TKJElectronics/SerialGLCD/PCB/Images for Gerber files/SerialGLCD.boardoutline.ger.png

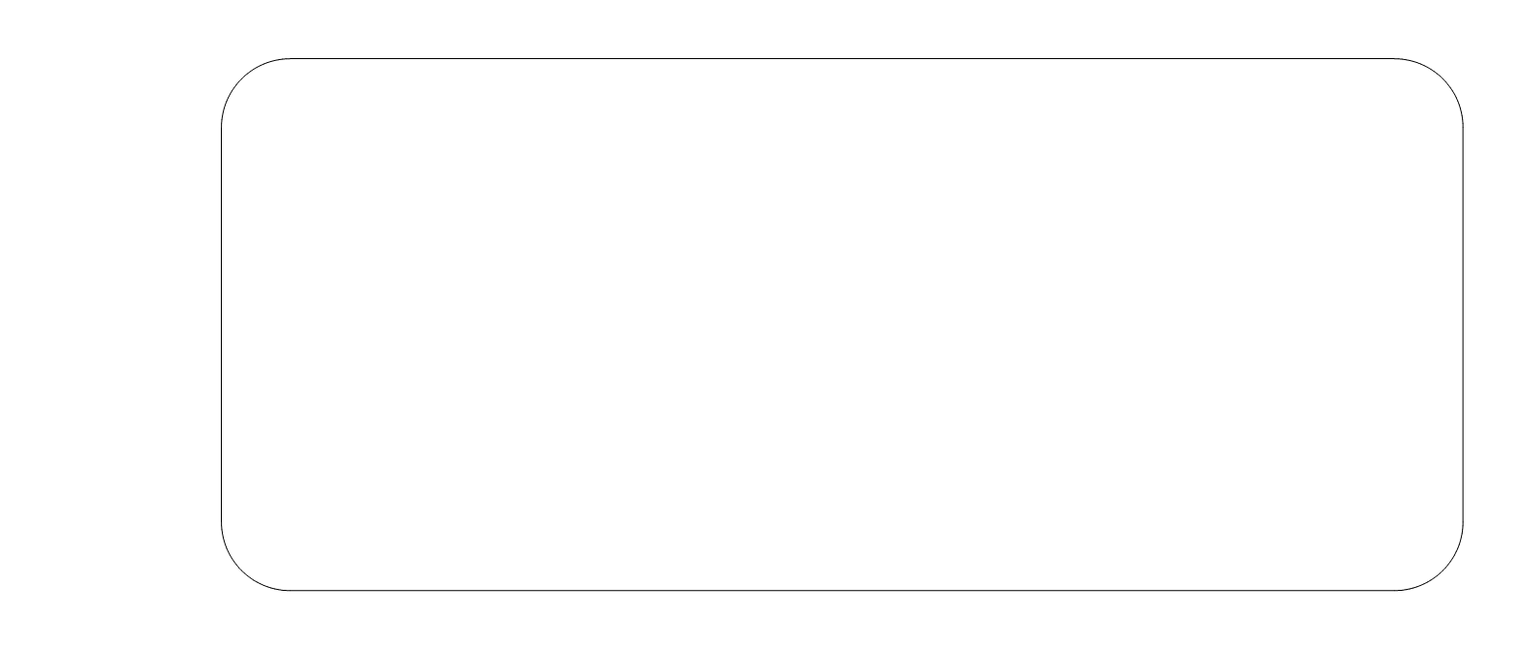
PCB/Images for Gerber files/SerialGLCD.boardoutline.ger.png
